RBEGamer/SimpleLORAWeatherstation/documenation/images/2021-10-14 20.19.17.jpg

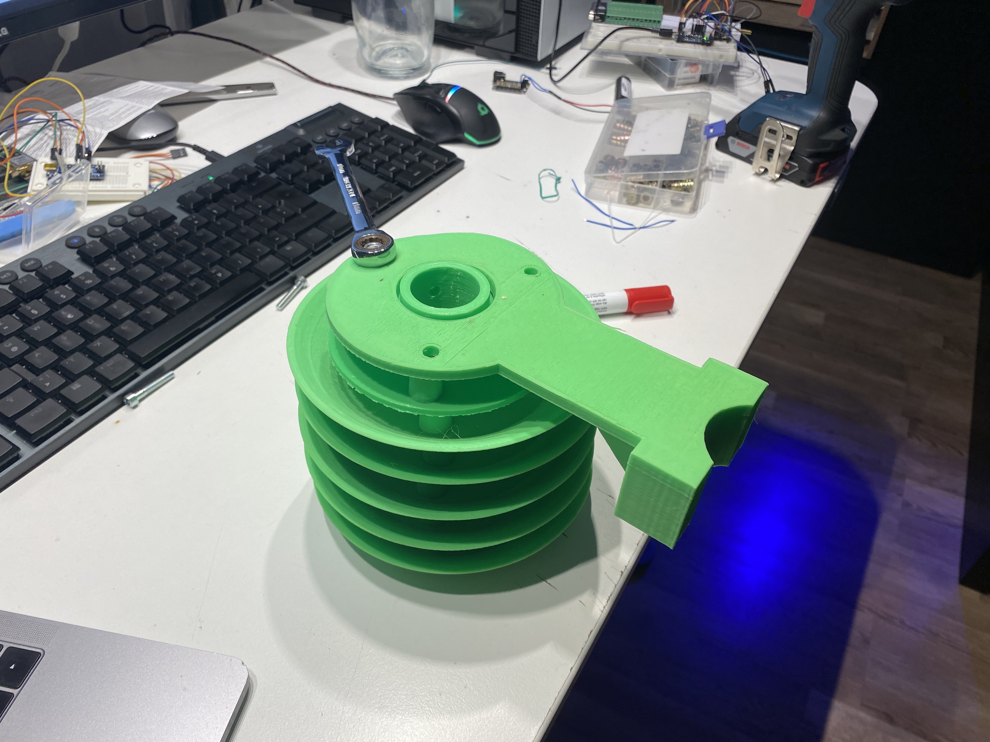
documenation/images/2021-10-14 20.19.17.jpg
