RBEGamer/SimpleLORAWeatherstation/documenation/images/2021-10-15 10.45.44.jpg

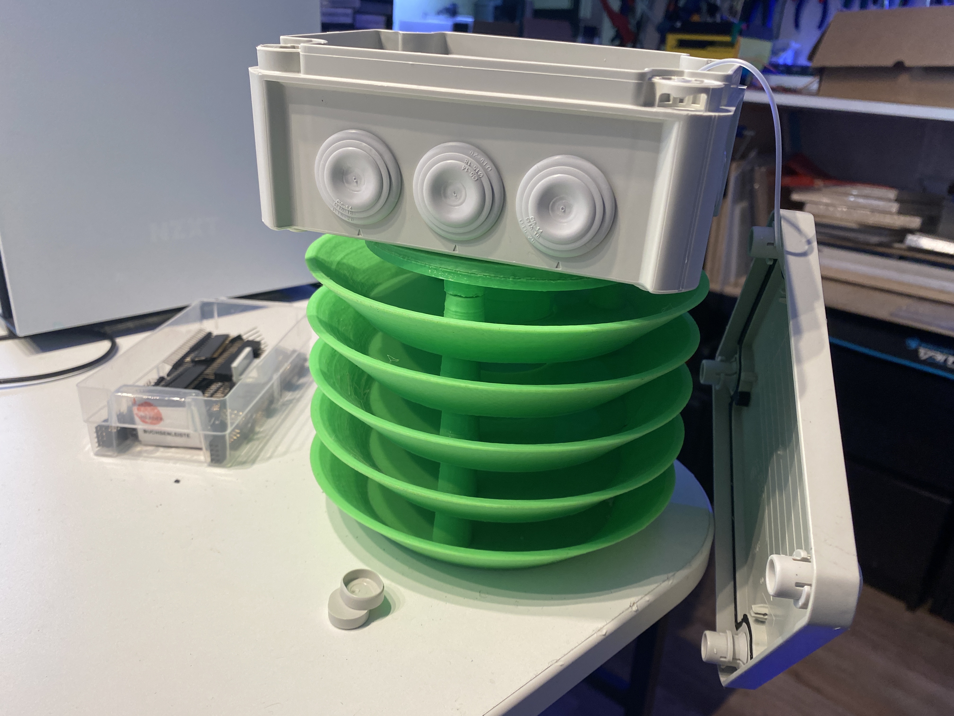
documenation/images/2021-10-15 10.45.44.jpg
