RBEGamer/SimpleLORAWeatherstation/documenation/images/2021-10-15 12.31.02.jpg

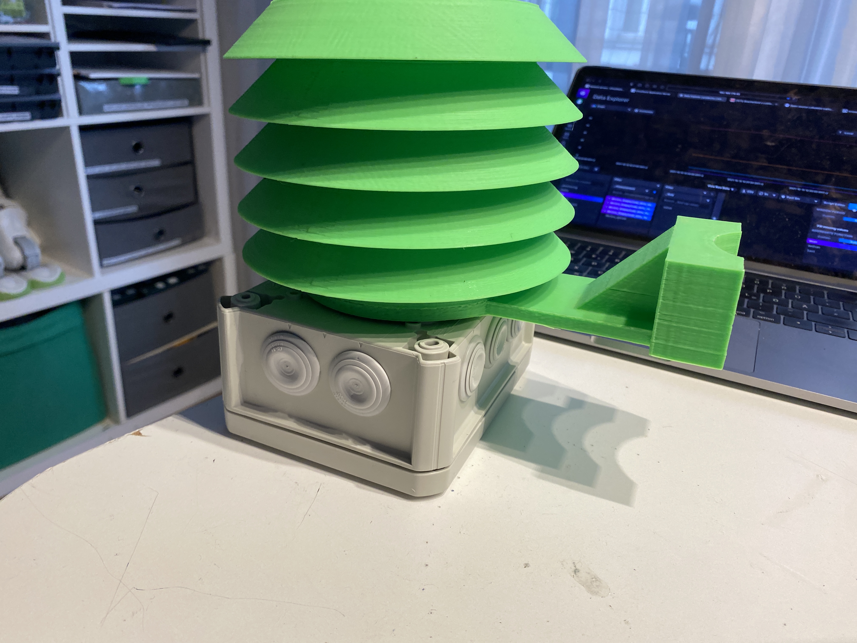
documenation/images/2021-10-15 12.31.02.jpg
