RBEGamer/SimpleLORAWeatherstation/documenation/images/2021-10-15 10.45.38.jpg

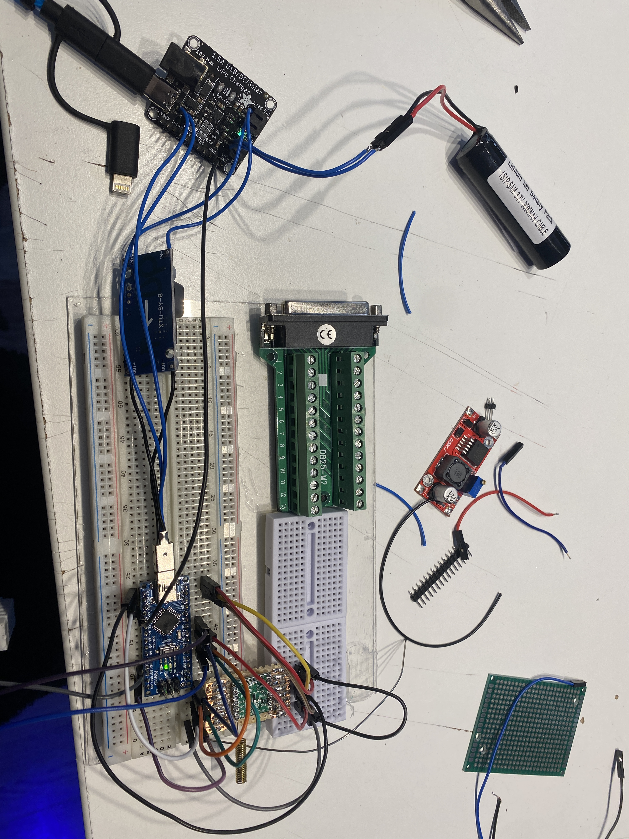
documenation/images/2021-10-15 10.45.38.jpg
