RBEGamer/SimpleLORAWeatherstation/documenation/images/2021-10-15 10.45.41.jpg

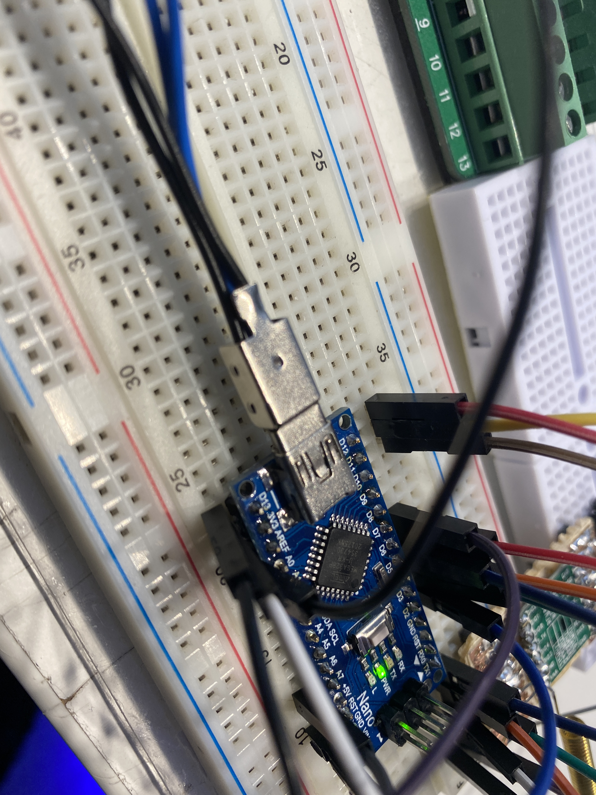
documenation/images/2021-10-15 10.45.41.jpg
